QC20/TinyTV/hardware/3d-print/images/20211106_115254.jpg

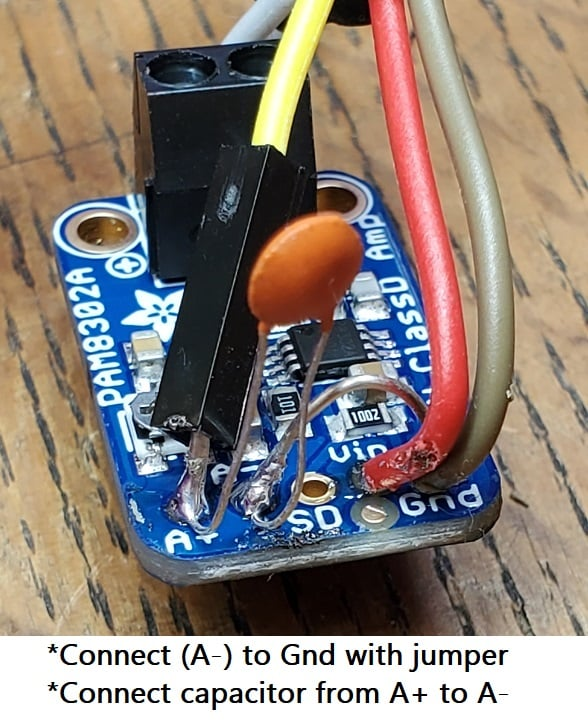
hardware/3d-print/images/20211106_115254.jpg
