QC20/TinyTV/hardware/3d-print/images/Model_back.png

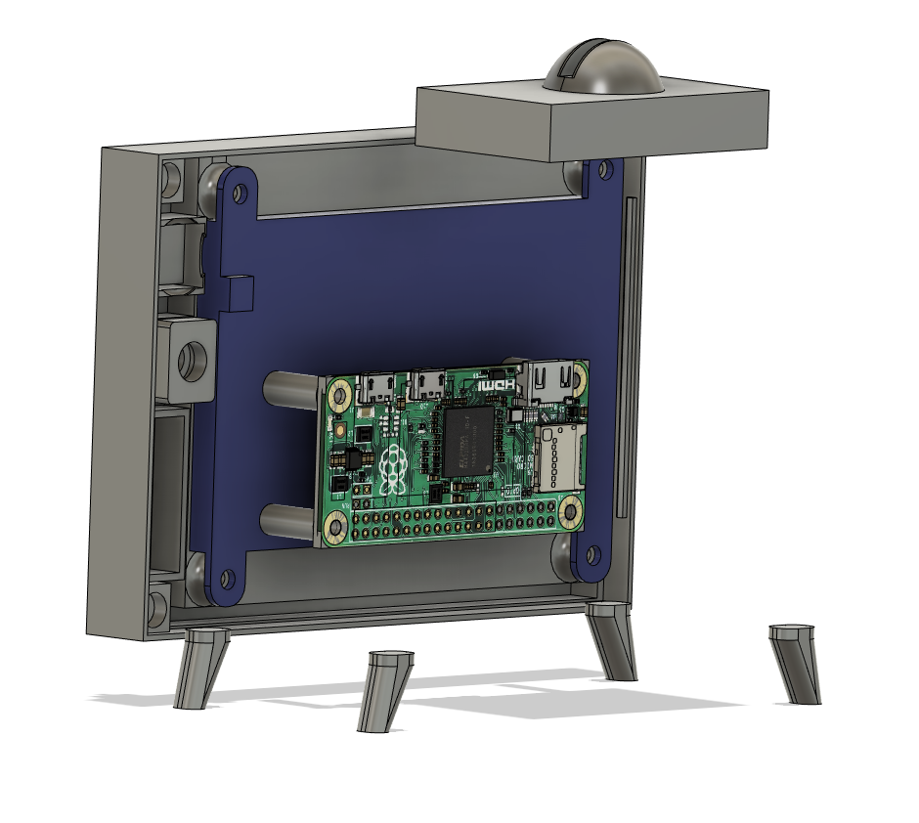
hardware/3d-print/images/Model_back.png
