QC20/TinyTV/hardware/3d-print/images/Model_front.png

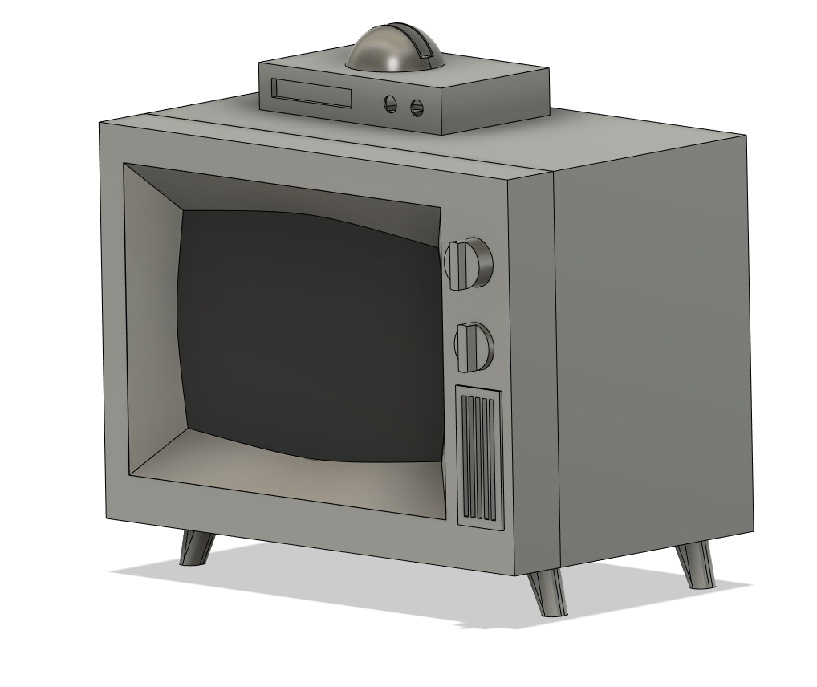
hardware/3d-print/images/Model_front.png
