QC20/TinyTV/hardware/3d-print/images/Pic1_sml.jpg

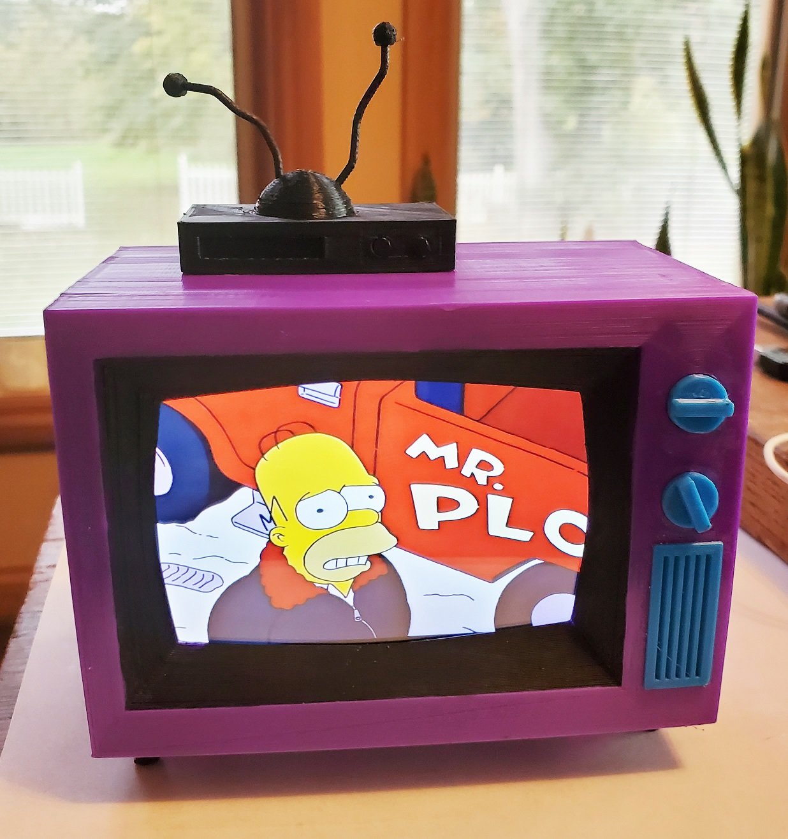
hardware/3d-print/images/Pic1_sml.jpg
