QC20/TinyTV/hardware/3d-print/images/Pic2_sml.jpg

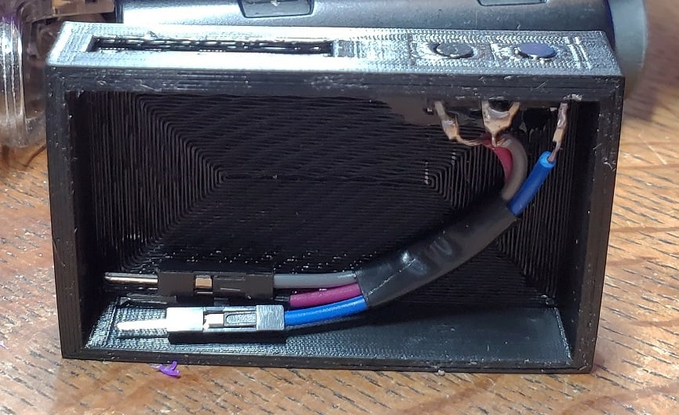
hardware/3d-print/images/Pic2_sml.jpg
