QC20/TinyTV/hardware/3d-print/images/Pic3_sml.jpg

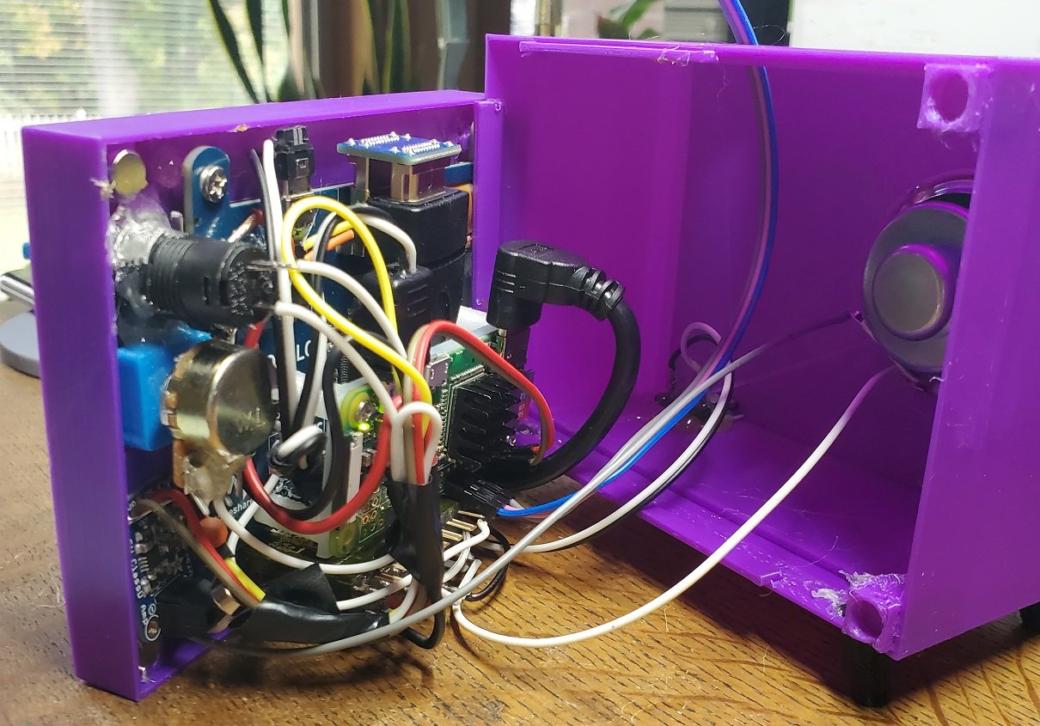
hardware/3d-print/images/Pic3_sml.jpg
