QC20/TinyTV/hardware/3d-print/images/Pic4_sml.jpg

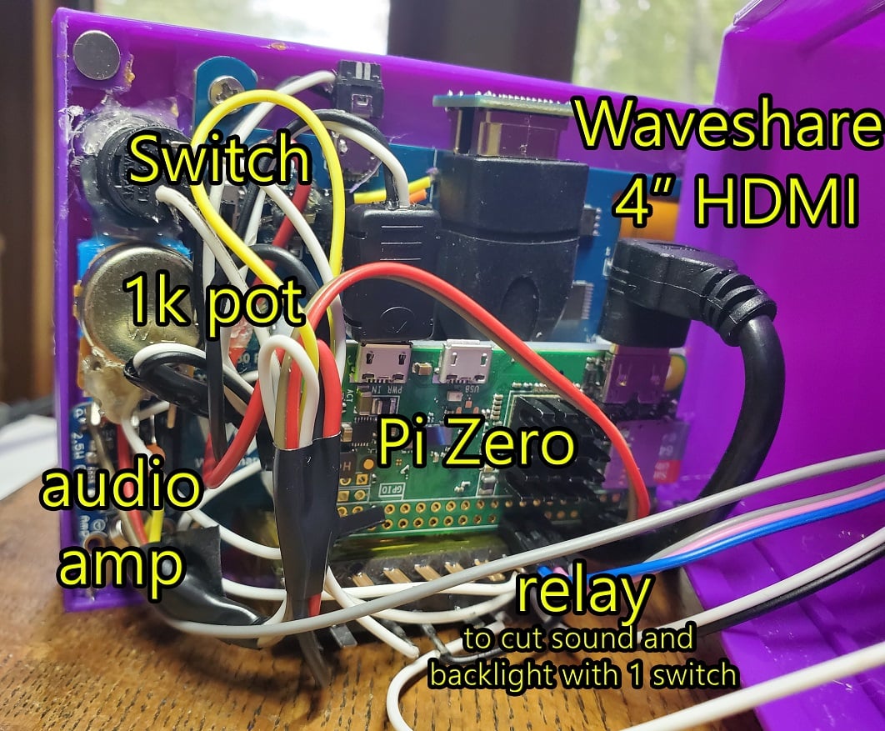
hardware/3d-print/images/Pic4_sml.jpg
