QC20/TinyTV/hardware/3d-print/images/Pic5_sml.jpg

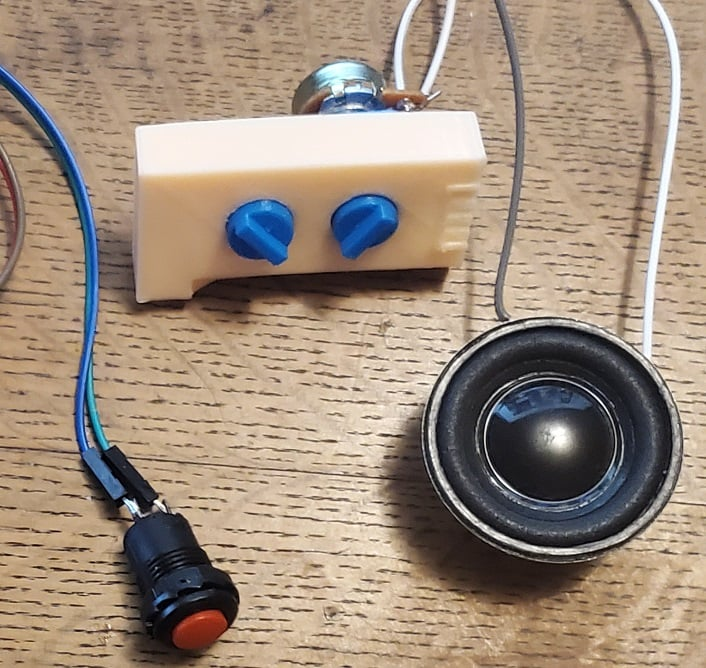
hardware/3d-print/images/Pic5_sml.jpg
