QC20/TinyTV/hardware/3d-print/images/standoff.png

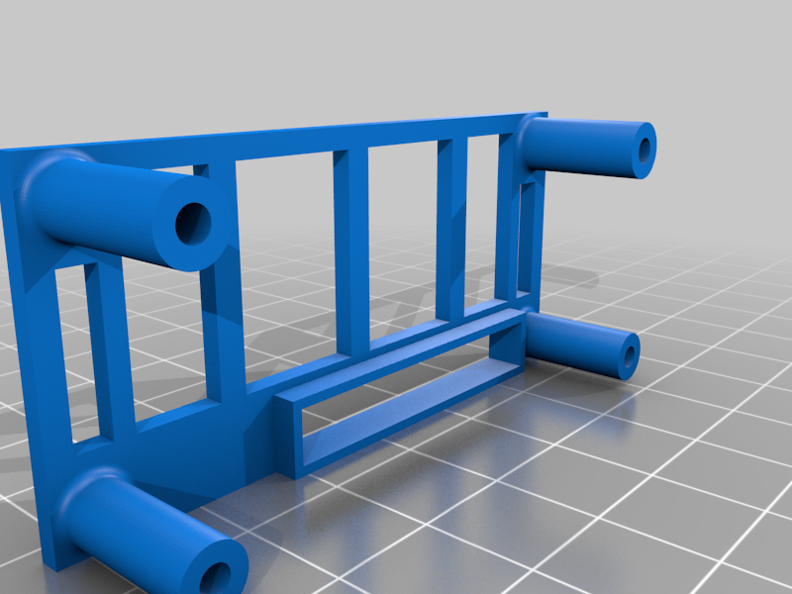
hardware/3d-print/images/standoff.png
