QC20/TinyTV/hardware/3d-print/images/STV_Body.png

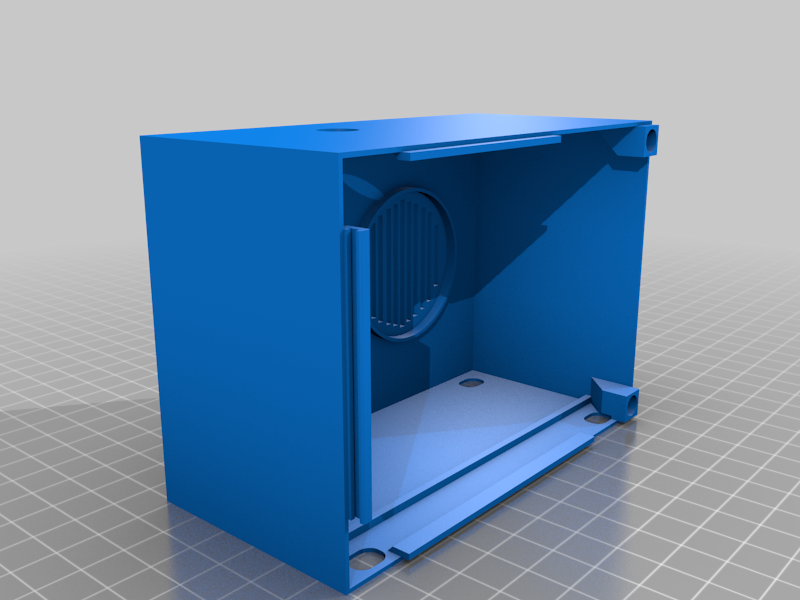
hardware/3d-print/images/STV_Body.png
