QC20/TinyTV/hardware/3d-print/images/STV_Bodypurple.png

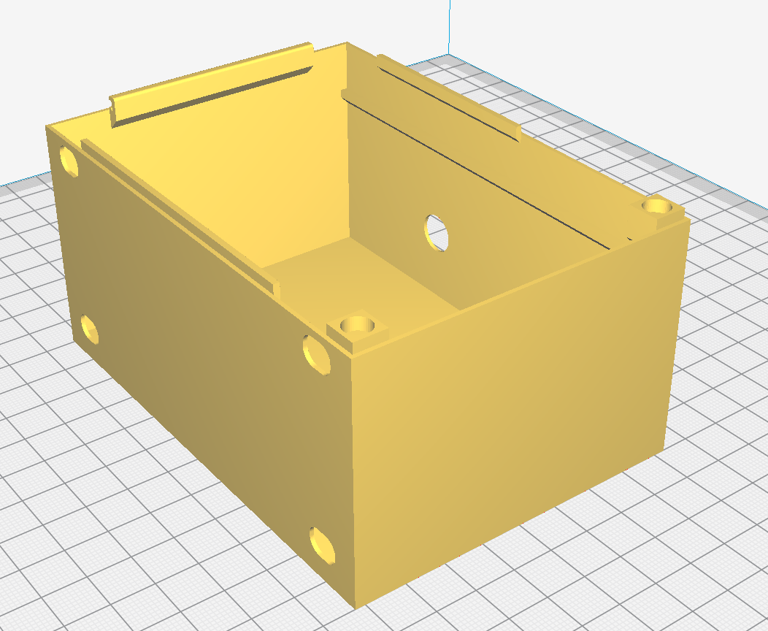
hardware/3d-print/images/STV_Bodypurple.png
