QC20/TinyTV/hardware/3d-print/images/STV_Front_insert.png

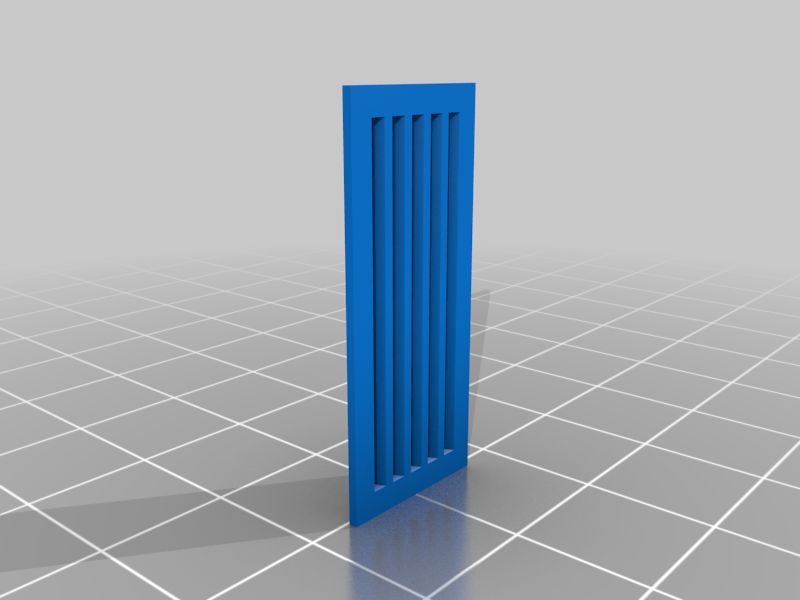
hardware/3d-print/images/STV_Front_insert.png
