QC20/TinyTV/hardware/3d-print/images/STV_Leg.png

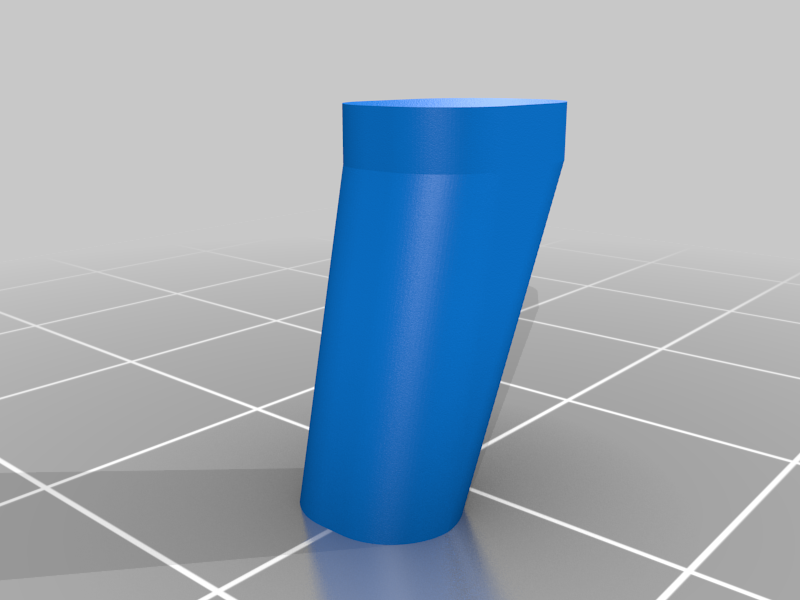
hardware/3d-print/images/STV_Leg.png
