QC20/TinyTV/hardware/3d-print/images/STV_Pknob.png

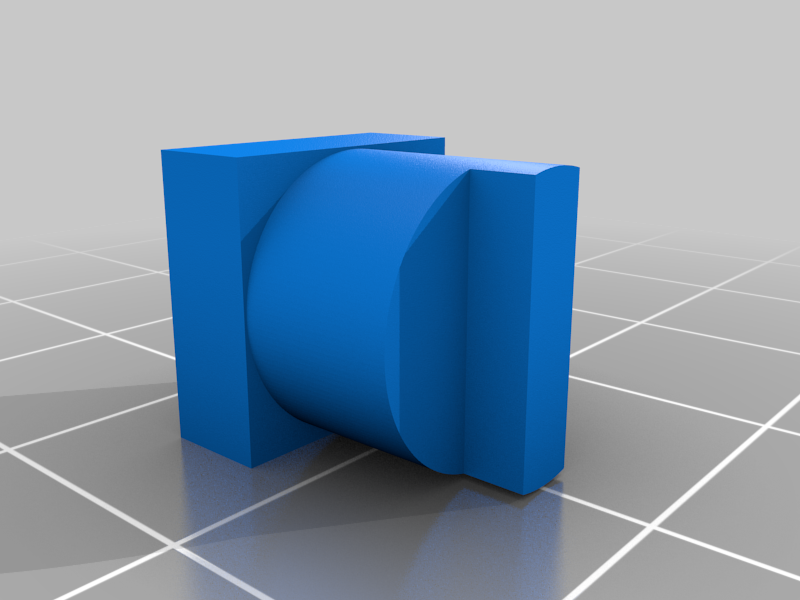
hardware/3d-print/images/STV_Pknob.png
