QC20/TinyTV/hardware/3d-print/images/STV_VCR_legs_Antblack.png

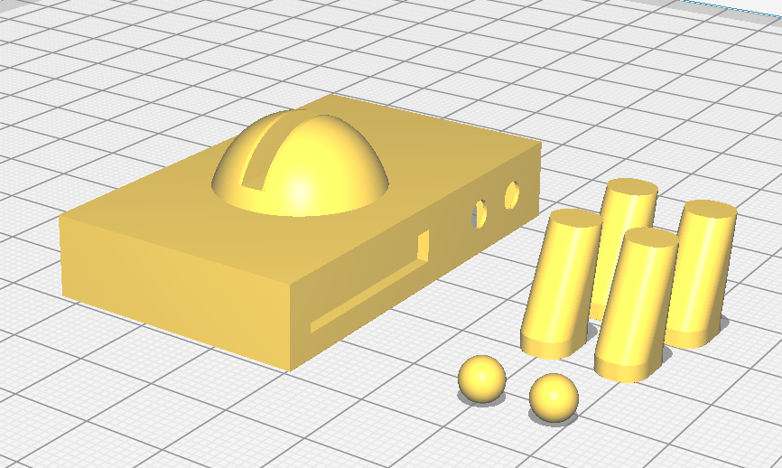
hardware/3d-print/images/STV_VCR_legs_Antblack.png
