QC20/TinyTV/hardware/3d-print/images/STV_Vknob_Base.png

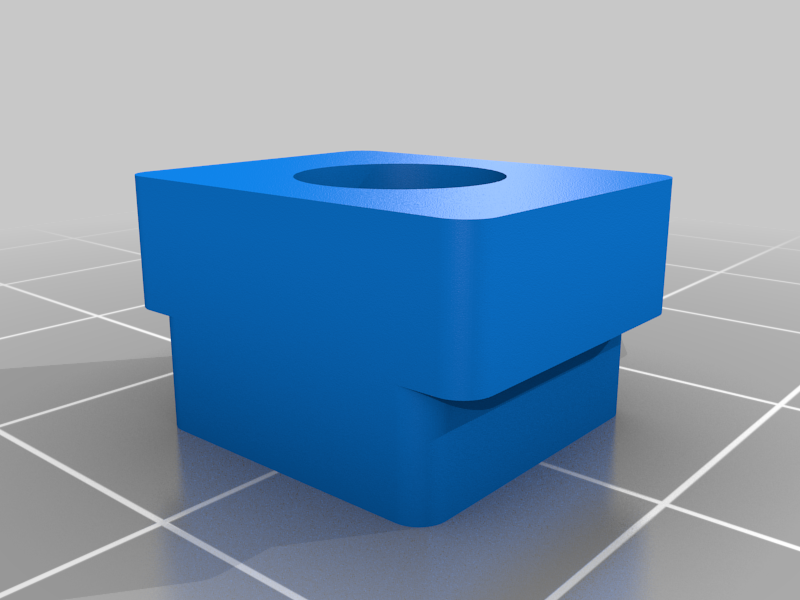
hardware/3d-print/images/STV_Vknob_Base.png
