QC20/TinyTV/hardware/3d-print/images/STVmod_VCR_solid_buttons.png

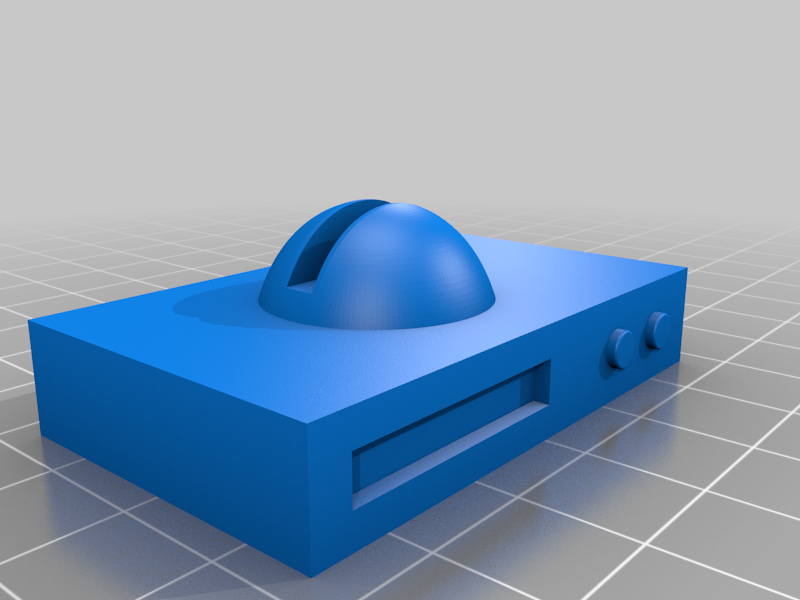
hardware/3d-print/images/STVmod_VCR_solid_buttons.png
